davidmpye/VFD/firmware/src/Clock.cpp

#include "Clock.h"

Clock::Clock() {


}

Clock::~Clock() {


}

void Clock::begin() {

    bool didReset = false;


      //Button 1
    pinMode(D0, INPUT);
    //Button 2
    pinMode(D5, INPUT);
    //Button 3
    pinMode(3, INPUT);
    //Button 4
    pinMode(1, INPUT);

    SPIFFS.begin();

    configManager.begin();

    //If you hold down Button 1 and Button 2 at powerup, it will resetToDefaults
    if (digitalRead(D0) == 0 && digitalRead(D5) == 0) {
      didReset = true;
      configManager.resetToDefaults();
    }

    display.setConfigManager(&configManager);
    display.begin();

    if (didReset) {
      //Display message to user confirming reset.
      display.scrollMessage("RESET", 4);
    }

    configTime(configManager.data.disp_timezone.c_str(), "pool.ntp.org");
  

    //No need to call wire.begin because rtc.begin calls it.
    //Init RTC.
    //This does occasionally fail so give it 10 attempts.
    bool rtcOk;
    for (int i=0; i<10; ++i) {
      delay(250);
      rtcOk = rtc.begin();
      if (rtcOk) break;
      //Final failure
    }

    if (!rtcOk) {
        display.scrollMessage("RTC ERR", 4);
    }

    setupWifi();

    //webHandler.setConfigManager(&configManager);
    //webHandler.begin();

    display.scrollMessage(configManager.data.disp_welcomemsg.c_str(), 4);

    buttonHandler.setConfigManager(&configManager);
    buttonHandler.begin(D0, D5, 3, 1, &display);
}

void Clock::loop() {
    static int lastSec = -1;
    DateTime t = rtc.now();
    //If the time has moved forward, we will update the display:
    if (t.second() != lastSec) {
       lastSec = t.second();
       display.displayTime(t);
    }

    display.update();

    handleButtonEvent(buttonHandler.poll());
    //webHandler.handleEvents();
    //MDNS responder
    MDNS.update();

    //Handle any other events.
    yield();
}

void Clock::checkNTP() {
  timeval tv;
  if(WiFi.status() == WL_CONNECTED) {
      gettimeofday(&tv, nullptr);
      time_t now = time(nullptr);
      rtc.adjust(DateTime(1900 + localtime(&now)->tm_year, 1+localtime(&now)->tm_mon, localtime(&now)->tm_mday, localtime(&now)->tm_hour, localtime(&now)->tm_min, localtime(&now)->tm_sec));
     }
}


void Clock::setRTC() {
  DateTime t = rtc.now(); //This will get the default time from above.
  tmElements_t y = buttonHandler.getDate(&t);
  tmElements_t x  = buttonHandler.getTime(&t);
  //Set the time
  rtc.adjust(DateTime(y.Year + 1970, y.Month, y.Day, x.Hour, x.Minute, x.Second));
}


void Clock::setupWifi() {
  if (configManager.data.wifi_mode == WIFI_STANDALONE) {
    //Set up as a standlone hotspot
    WiFi.mode(WIFI_AP);
    WiFi.softAPConfig (configManager.data.wifi_ip, configManager.data.wifi_gateway, configManager.data.wifi_netmask);
    WiFi.softAP(configManager.data.wifi_ssid, configManager.data.wifi_pw);
  }
  else {
    //Join the desired network
    if (configManager.data.wifi_ip_mode == WIFI_IP_STATIC) {
        //set the IP details.
        WiFi.config(configManager.data.wifi_ip, configManager.data.wifi_gateway, configManager.data.wifi_netmask);
    }
    WiFi.begin(configManager.data.wifi_ssid, configManager.data.wifi_pw);
  }
  //If we have an MDNS name configured, enable that.
  if (configManager.data.wifi_mdns_name != "") {
    MDNS.begin(configManager.data.wifi_mdns_name);
    MDNS.addService("http", "tcp", 80);
  }
}

void Clock::handleButtonEvent(BUTTON_EVENT e) {
  switch(e) {
    case BUTTON_A_SHORTPRESS:
      display.displayDate(rtc.now());
      display.updateTubes();
      delay(2000);
      break;

    case BUTTON_A_LONGPRESS:
      setRTC();
      break;

    case BUTTON_C_SHORTPRESS:
      if (configManager.data.disp_timeformat == 2) {
        configManager.data.disp_timeformat = 0;
      }
      else configManager.data.disp_timeformat++;

    case BUTTON_B_SHORTPRESS:
        if (configManager.data.led_color_mode == 2)
          configManager.data.led_color_mode = 0;
        else configManager.data.led_color_mode++;
          break;

      case BUTTON_C_LONGPRESS:
        //Display the brightness level the LDR is seeing.
        display.displayInt(analogRead(A0));
        display.update();
        delay(1000);
        break;

      case BUTTON_D_LONGPRESS:
        //Test the segments of the display.
        display.test();
        display.update();
        delay(1000);
        break;

        default:
          break;
  }
  // Only save relevant changes
  if(e & (BUTTON_B_SHORTPRESS | BUTTON_C_SHORTPRESS)) configManager.saveToFlash();
}
