davidmpye/VFD/firmware/src/Display.h

/*
    VFD clock firmware (c) 2018 David Pye <davidmpye@gmail.com>

    http://www.davidmpye.com/VFD

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
    You should have received a copy of the GNU General Public License
    along with this program.  If not, see <https://www.gnu.org/licenses/>.
*/

#ifndef __DISPLAY_H__
#define __DISPLAY_H__

#define FASTLED_ALLOW_INTERRUPTS 0

#include <FastLED.h>
#include <Time.h>
#include <Timezone.h>
#include <RTClib.h>

#include "Config.h"
#include "ConfigManager.h"

class Display {
  public:

    Display();
    ~Display();

    void begin();

    void setConfigManager(ConfigManager *);

    //Higher level functions
    //Displays the current time on the tubes, using TIME_MODE format
    void displayTime(DateTime t);
    //Displays the current date on the tubes, using the DATE_MODE format
    void displayDate(DateTime d);
    void displayInt(int val, int base);
    //defaults to base 10
    void displayInt(int val);

    void hello(); //displays the word hello as a welcome message.
    void scrollMessage(const char *message, int speed);

    void clear(); //clears display and data
    void blank(); //clears the display, but doesnt clear data, so calling refreshDisplay will unblank it.

    void setBrightness(); //Sets the brightness of the tubes (and LEDs) - for the tubes, it uses PWM, for the LEDs it uses Fastled's setBrightness.

    void update(); //The display's 'main loop'

    void updateTubes();

    void test(); //Lights all segments on all tubes

    //Lower level manipulations.
    void setTubeByte(int tube, uint8_t b) ;
    void setTubeNumber(int tube, uint8_t n ) ;
    void setTubeChar(int tube, char c);
    void setTubeDP(int tube, bool p);

    const uint8_t getTubeNumber(int tube);
    const uint8_t getTubeByte(int tube);
    const char getTubeChar(int tube);

  private:
    void fillLEDData();
    void updateLEDs();
    void updateBrightness();

  ConfigManager *configManager;

  uint8_t brightness;
  bool ledsOff;
  uint8_t _displayData[NUM_TUBES];

  CRGB leds[NUM_LEDS];

  uint8_t _fontTable[95] = {
    0x00,  // space
    0x82,  // !
    0x22,  // "
    0x00,  // #
    0x00,  // $
    0x00,  // %
    0x00,  // &
    0x02,  // '
    0x39,  // (
    0x0F,  // )
    0x00,  // *
    0x00,  // +
    0x04,  // ,
    0x40,  // -
    0x80,  // .
    0x00,  // /
    0x3F,  // 0
    0x06,  // 1
    0x5B,  // 2
    0x4F,  // 3
    0x66,  // 4
    0x6D,  // 5
    0x7D,  // 6
    0x07,  // 7
    0x7F,  // 8
    0x6F,  // 9
    0x00,  // :
    0x00,  // ;
    0x00,  // <
    0x09,  // =
    0x00,  // >
    0x53,  // ?
    0x00,  // @
    0x77,  // A
    0x7C,  // B
    0x39,  // C
    0x5E,  // D
    0x79,  // E
    0x71,  // F
    0x3D,  // G
    0x76,  // H
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
  };
};

#endif
